Sharefox/SpO2-HB/Code/HandCopy/Inc/home_data.h

/*
 * Generated with 'Image to C converter for Discovery' Version 1.0a
 * Author: Dams Wim                                    Date: Dec 10 2016
 *
 * Generated from: E:/Glenn/OneDrive/Bureaublad/School/Thomasmore/PE2/home.jpg
 * Date Generated: 21 May 2021  1:06:10
 */

#ifndef HOME_H_
#define HOME_H_

#define HOME_DATA_X_PIXEL   160
#define HOME_DATA_Y_PIXEL   80
#define HOME_DATA_TOT_PIXEL 12800
#define HOME_DATA_FORMAT    LTDC_PIXEL_FORMAT_RGB565

const unsigned short HOME_DATA[12800] = {
 0x31cb, 0x31cb, 0x31cb, 0x31cb, 0x31cb, 0x31cb, 0x31cb, 0x31cb, 0x31cb, 0x31cb, 
 0x31cb, 0x31cb, 0x31cb, 0x31cb, 0x31cb, 0x31cb, 0x31cb, 0x31cb, 0x31cb, 0x31cb, 
 0x31cb, 0x31cb, 0x31cb, 0x31cb, 0x31cb, 0x31cb, 0x31cb, 0x31cb, 0x31cb, 0x31cb, 
 0x31cb, 0x31cb, 0x31cb, 0x31cb, 0x31cb, 0x31cb, 0x31cb, 0x31cb, 0x31cb, 0x31cb, 
 0x31cb, 0x31cb, 0x31cb, 0x31cb, 0x31cb, 0x31cb, 0x31cb, 0x31cb, 0x31cb, 0x31cb, 
 0x31cb, 0x31cb, 0x31cb, 0x31cb, 0x31cb, 0x31cb, 0x31cb, 0x31cb, 0x31cb, 0x31cb, 
 0x31cb, 0x31cb, 0x31cb, 0x31cb, 0x31cb, 0x31cb, 0x31cb, 0x31cb, 0x31cb, 0x31cb, 
 0x31cb, 0x31cb, 0x31cb, 0x31cb, 0x31cb, 0x31cb, 0x31cb, 0x31cb, 0x31cb, 0x31cb, 
 0x31cb, 0x31cb, 0x31cb, 0x31cb, 0x31cb, 0x31cb, 0x31cb, 0x31cb, 0x31cb, 0x31cb, 
 0x31cb, 0x31cb, 0x31cb, 0x31cb, 0x31cb, 0x31cb, 0x31cb, 0x31cb, 0x31cb, 0x31cb, 
 0x31cb, 0x31cb, 0x31cb, 0x31cb, 0x31cb, 0x31cb, 0x31cb, 0x31cb, 0x31cb, 0x31cb, 
 0x31cb, 0x31cb, 0x31cb, 0x31cb, 0x31cb, 0x31cb, 0x31cb, 0x31cb, 0x31cb, 0x31cb, 
 0x31cb, 0x31cb, 0x31cb, 0x31cb, 0x31cb, 0x31cb, 0x31cb, 0x31cb, 0x31cb, 0x31cb, 
 0x31cb, 0x31cb, 0x31cb, 0x31cb, 0x31cb, 0x31cb, 0x31cb, 0x31cb, 0x31cb, 0x31cb, 
 0x31cb, 0x31cb, 0x31cb, 0x31cb, 0x31cb, 0x31cb, 0x31cb, 0x31cb, 0x31cb, 0x31cb, 
 0x31cb, 0x31cb, 0x31cb, 0x31cb, 0x31cb, 0x31cb, 0x31cb, 0x31cb, 0x31cb, 0x31cb, 
 0x31cb, 0x31cb, 0x31cb, 0x31cb, 0x31cb, 0x31cb, 0x31cb, 0x31cb, 0x31cb, 0x31cb, 
 0x31cb, 0x31cb, 0x31cb, 0x31cb, 0x31cb, 0x31cb, 0x31cb, 0x31cb, 0x31cb, 0x31cb, 
 0x31cb, 0x31cb, 0x31cb, 0x31cb, 0x31cb, 0x31cb, 0x31cb, 0x31cb, 0x31cb, 0x31cb, 
 0x31cb, 0x31cb, 0x31cb, 0x31cb, 0x31cb, 0x31cb, 0x31cb, 0x31cb, 0x31cb, 0x31cb, 
 0x31cb, 0x31cb, 0x31cb, 0x31cb, 0x31cb, 0x31cb, 0x31cb, 0x31cb, 0x31cb, 0x31cb, 
 0x31cb, 0x31cb, 0x31cb, 0x31cb, 0x31cb, 0x31cb, 0x31cb, 0x31cb, 0x31cb, 0x31cb, 
 0x31cb, 0x31cb, 0x31cb, 0x31cb, 0x31cb, 0x31cb, 0x31cb, 0x31cb, 0x31cb, 0x31cb, 
 0x31cb, 0x31cb, 0x31cb, 0x31cb, 0x31cb, 0x31cb, 0x31cb, 0x31cb, 0x31cb, 0x31cb, 
 0x31cb, 0x31cb, 0x31cb, 0x31cb, 0x31cb, 0x31cb, 0x31cb, 0x31cb, 0x31cb, 0x31cb, 
 0x31cb, 0x31cb, 0x31cb, 0x31cb, 0x31cb, 0x31cb, 0x31cb, 0x31cb, 0x31cb, 0x31cb, 
 0x31cb, 0x31cb, 0x31cb, 0x31cb, 0x31cb, 0x31cb, 0x31cb, 0x31cb, 0x31cb, 0x31cb, 
 0x31cb, 0x31cb, 0x31cb, 0x31cb, 0x31cb, 0x31cb, 0x31cb, 0x31cb, 0x31cb, 0x31cb, 
 0x31cb, 0x31cb, 0x31cb, 0x31cb, 0x31cb, 0x31cb, 0x31cb, 0x31cb, 0x31cb, 0x31cb, 
 0x31cb, 0x31cb, 0x31cb, 0x31cb, 0x31cb, 0x31cb, 0x31cb, 0x31cb, 0x31cb, 0x31cb, 
 0x31cb, 0x31cb, 0x31cb, 0x31cb, 0x31cb, 0x31cb, 0x31cb, 0x31cb, 0x31cb, 0x31cb, 
 0x31cb, 0x31cb, 0x31cb, 0x31cb, 0x31cb, 0x31cb, 0x31cb, 0x31cb, 0x31cb, 0x31cb, 
 0x31cb, 0x31cb, 0x31cb, 0x31cb, 0x31cb, 0x31cb, 0x31cb, 0x31cb, 0x31cb, 0x31cb, 
 0x31cb, 0x31cb, 0x31cb, 0x31cb, 0x31cb, 0x31cb, 0x31cb, 0x31cb, 0x31cb, 0x31cb, 
 0x31cb, 0x31cb, 0x31cb, 0x31cb, 0x31cb, 0x31cb, 0x31cb, 0x31cb, 0x31cb, 0x31cb, 
 0x31cb, 0x31cb, 0x31cb, 0x31cb, 0x31cb, 0x31cb, 0x31cb, 0x31cb, 0x31cb, 0x31cb, 
 0x31cb, 0x31cb, 0x31cb, 0x31cb, 0x31cb, 0x31cb, 0x31cb, 0x31cb, 0x31cb, 0x31cb, 
 0x31cb, 0x31cb, 0x31cb, 0x31cb, 0x31cb, 0x31cb, 0x31cb, 0x31cb, 0x31cb, 0x31cb, 
 0x31cb, 0x31cb, 0x31cb, 0x31cb, 0x31cb, 0x31cb, 0x31cb, 0x31cb, 0x31cb, 0x31cb, 
 0x31cb, 0x31cb, 0x31cb, 0x31cb, 0x31cb, 0x31cb, 0x31cb, 0x31cb, 0x31cb, 0x31cb, 
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
 
};

#endif /* HOME_H_ */
