Sharefox/SpO2-HB/Code/HandCopy/Src/stm32wbxx_it.c

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

/* Includes ------------------------------------------------------------------*/
#include "main.h"
#include "stm32wbxx_it.h"
/* USER CODE BEGIN Includes */
#include "app_common.h"
/* USER CODE END Includes */

/* External variables --------------------------------------------------------*/
extern IPCC_HandleTypeDef hipcc;
extern RTC_HandleTypeDef hrtc;
/******************************************************************************/
/*           Cortex Processor Interruption and Exception Handlers          */
/******************************************************************************/
/**
  * @brief This function handles Non maskable interrupt.
  */
void NMI_Handler(void)
{
  /* USER CODE BEGIN NonMaskableInt_IRQn 1 */
  while (1)
  {
  }
  /* USER CODE END NonMaskableInt_IRQn 1 */
}

/**
  * @brief This function handles Hard fault interrupt.
  */
void HardFault_Handler(void)
{
  /* USER CODE BEGIN HardFault_IRQn 0 */
	__asm volatile (
	    " movs r0,#4       \n"
	    " movs r1, lr      \n"
	    " tst r0, r1       \n"
	    " beq _MSP         \n"
	    " mrs r0, psp      \n"
	    " b _HALT          \n"
	  "_MSP:               \n"
	    " mrs r0, msp      \n"
	  "_HALT:              \n"
	    " ldr r1,[r0,#20]  \n"
	    " bkpt #0          \n"
	  );
  /* USER CODE END HardFault_IRQn 0 */
  while (1)
  {
  }
}

/**
  * @brief This function handles Memory management fault.
  */
void MemManage_Handler(void)
{
  while (1)
  {
  }
}

/**
  * @brief This function handles Prefetch fault, memory access fault.
  */
void BusFault_Handler(void)
{
  while (1)
  {
  }
}

/**
  * @brief This function handles Undefined instruction or illegal state.
  */
void UsageFault_Handler(void)
{
  while (1)
  {
  }
}

/**
  * @brief This function handles System service call via SWI instruction.
  */
void SVC_Handler(void)
{
}

/**
  * @brief This function handles Debug monitor.
  */
void DebugMon_Handler(void)
{
}

/**
  * @brief This function handles Pendable request for system service.
  */
void PendSV_Handler(void)
{
}

/**
  * @brief This function handles System tick timer.
  */
void SysTick_Handler(void)
{
  HAL_IncTick();
}

/******************************************************************************/
/* STM32WBxx Peripheral Interrupt Handlers                                    */
/* Add here the Interrupt Handlers for the used peripherals.                  */
/* For the available peripheral interrupt handler names,                      */
/* please refer to the startup file (startup_stm32wbxx.s).                    */
/******************************************************************************/

/**
  * @brief This function handles RTC wake-up interrupt through EXTI line 19.
  */
void RTC_WKUP_IRQHandler(void)
{
  HAL_RTCEx_WakeUpTimerIRQHandler(&hrtc);
}

/**
  * @brief This function handles EXTI line0 interrupt.
  */
void EXTI0_IRQHandler(void)
{
  HAL_GPIO_EXTI_IRQHandler(GPIO_PIN_0);
}

/**
  * @brief This function handles IPCC RX occupied interrupt.
  */
void IPCC_C1_RX_IRQHandler(void)
{
  HAL_IPCC_RX_IRQHandler(&hipcc);
}

/**
  * @brief This function handles IPCC TX free interrupt.
  */
void IPCC_C1_TX_IRQHandler(void)
{
  HAL_IPCC_TX_IRQHandler(&hipcc);
}

/**
  * @brief This function handles HSEM global interrupt.
  */
void HSEM_IRQHandler(void)
{
  HAL_HSEM_IRQHandler();
}

/************************ (C) COPYRIGHT STMicroelectronics *****END OF FILE****/
