Sharefox/SpO2-HB/Code/HandCopy/Inc/MAXCalc.h

/** \file algorithm.h ******************************************************
*
* Project: MAXREFDES117#
* Filename: algorithm.h
* Description: This module is the heart rate/SpO2 calculation algorithm header file
*
* Revision History:
*\n 1-18-2016 Rev 01.00 SK Initial release.
*\n
*
* --------------------------------------------------------------------
*
* This code follows the following naming conventions:
*
*\n char              ch_pmod_value
*\n char (array)      s_pmod_s_string[16]
*\n float             f_pmod_value
*\n int32_t           n_pmod_value
*\n int32_t (array)   an_pmod_value[16]
*\n int16_t           w_pmod_value
*\n int16_t (array)   aw_pmod_value[16]
*\n uint16_t          uw_pmod_value
*\n uint16_t (array)  auw_pmod_value[16]
*\n uint8_t           uch_pmod_value
*\n uint8_t (array)   auch_pmod_buffer[16]
*\n uint32_t          un_pmod_value
*\n int32_t *         pn_pmod_value
*
* ------------------------------------------------------------------------- */
/*******************************************************************************
* Copyright (C) 2015 Maxim Integrated Products, Inc., All Rights Reserved.
*
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
* Except as contained in this notice, the name of Maxim Integrated
* Products, Inc. shall not be used except as stated in the Maxim Integrated
* Products, Inc. Branding Policy.
*
* The mere transfer of this software does not imply any licenses
* of trade secrets, proprietary technology, copyrights, patents,
* trademarks, maskwork rights, or any other form of intellectual
* property whatsoever. Maxim Integrated Products, Inc. retains all
* ownership rights.
*******************************************************************************
*/

#ifndef SPO2_ALGORITHM_H_
#define SPO2_ALGORITHM_H_

#define FreqS 25    //sampling frequency
#define BUFFER_SIZE (FreqS * 4)
#define MA4_SIZE 4 // DONOT CHANGE

void maxim_heart_rate_and_oxygen_saturation(uint32_t *pun_ir_buffer, uint32_t n_ir_buffer_length, uint32_t *pun_red_buffer, uint32_t *pn_spo2, uint8_t *pch_spo2_valid, uint32_t *pn_heart_rate, uint8_t *pch_hr_valid);

void maxim_find_peaks( uint32_t *pn_locs, uint32_t *n_npks,  uint32_t  *pn_x, uint32_t n_size, uint32_t n_min_height, uint32_t n_min_distance, uint32_t n_max_num );
void maxim_peaks_above_min_height(uint32_t *pn_locs, uint32_t *n_npks,  uint32_t  *pn_x, uint32_t n_size, uint32_t n_min_height);
void maxim_remove_close_peaks(uint32_t *pn_locs, uint32_t *pn_npks, uint32_t *pn_x, uint32_t n_min_distance);
void maxim_sort_ascend(uint32_t  *pn_x, uint32_t n_size);
void maxim_sort_indices_descend(uint32_t  *pn_x, uint32_t *pn_indx, uint32_t n_size);

#endif /* ALGORITHM_H_ */
